phtoth/A320Overhead/Eletronics/Korry_Circuit/korry_circuit_3D_top.PNG

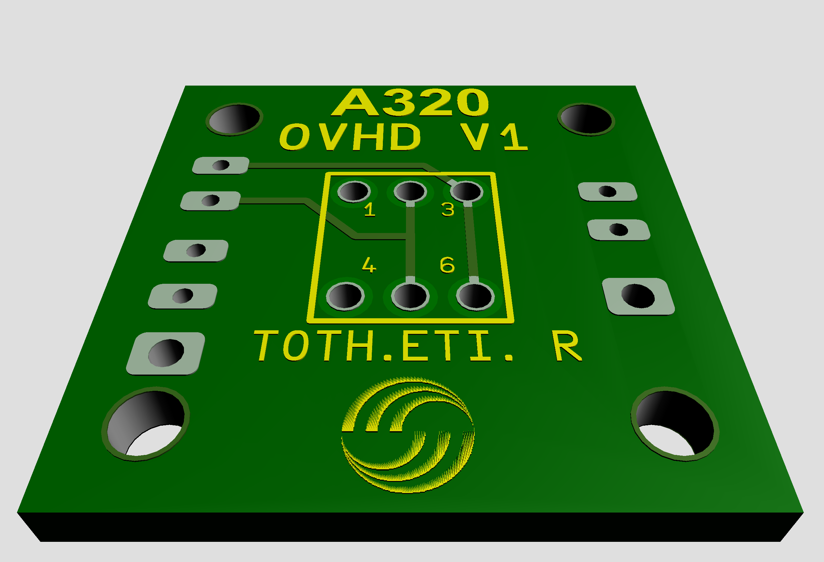
Eletronics/Korry_Circuit/korry_circuit_3D_top.PNG
