phtoth/A320Overhead/Images that Help/ard-mega-pro_io_zc_1024x1024.jpg

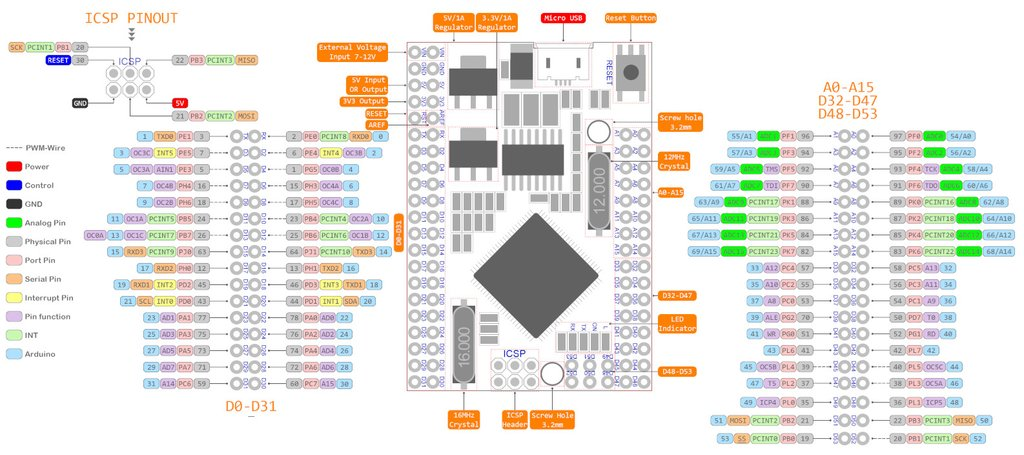
Images that Help/ard-mega-pro_io_zc_1024x1024.jpg
