phtoth/A320Overhead/Images that Help/chave_botao_7x7_des-500x500-product_popup.jpg

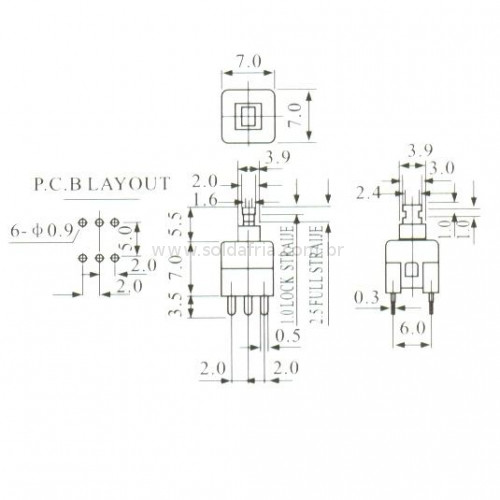
Images that Help/chave_botao_7x7_des-500x500-product_popup.jpg
