phtoth/A320Overhead/Images that Help/images.jpg

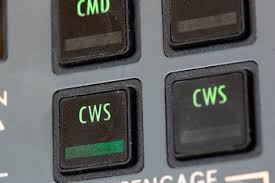
Images that Help/images.jpg
