phtoth/A320Overhead/Images that Help/IMG_1794.jpg

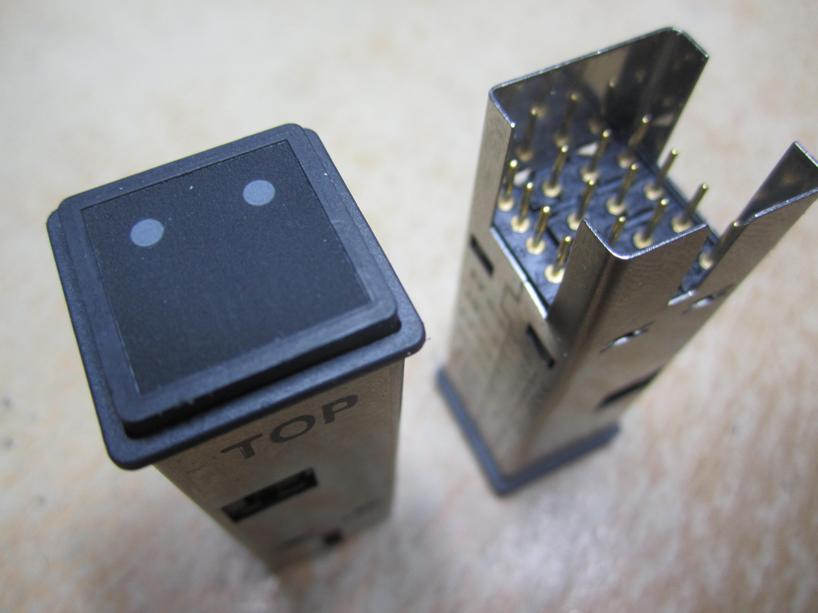
Images that Help/IMG_1794.jpg
