phtoth/A320Overhead/Images that Help/korry-announciator.jpg

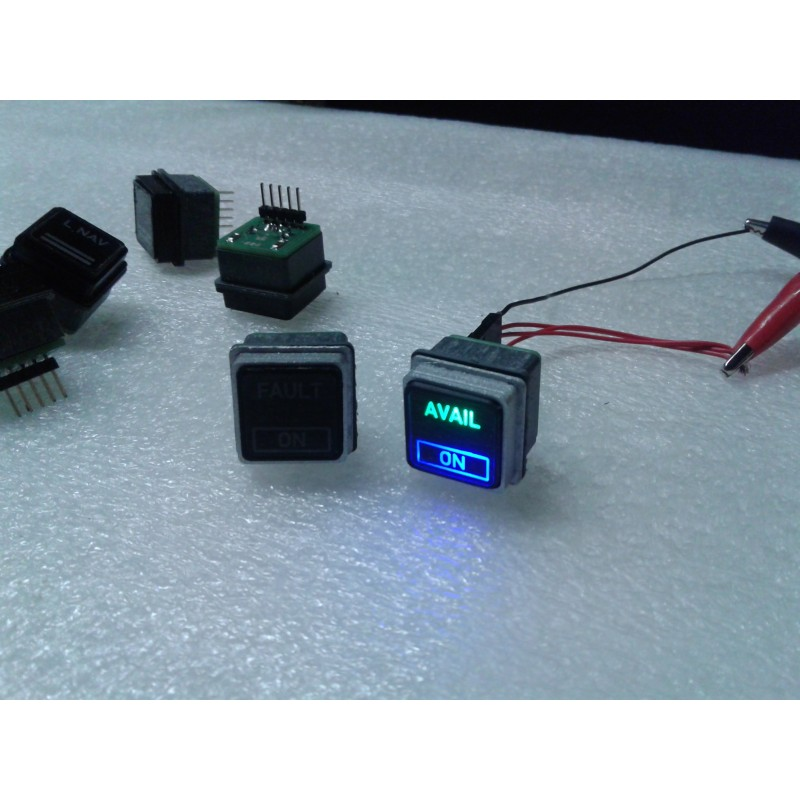
Images that Help/korry-announciator.jpg
