phtoth/A320Overhead/Images that Help/Korry-Switch-Inside-Render.png

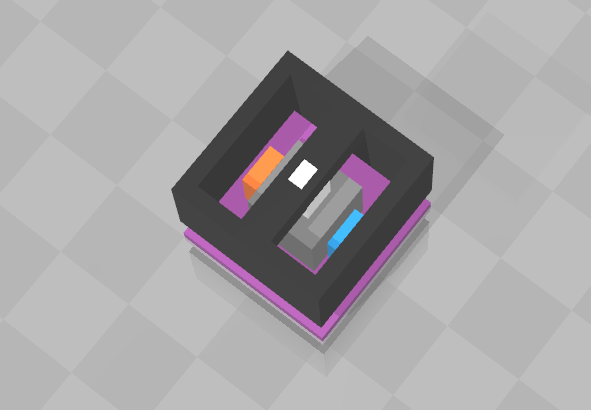
Images that Help/Korry-Switch-Inside-Render.png
