phtoth/A320Overhead/Images that Help/overhead_pic2.jpg

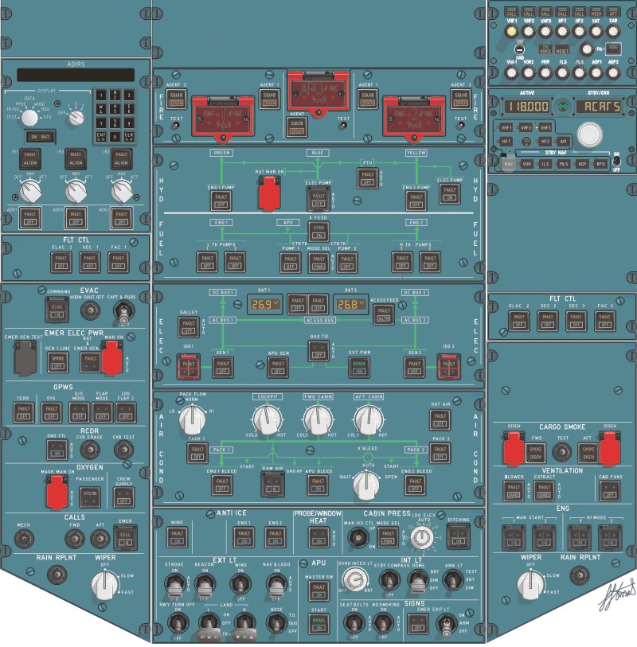
Images that Help/overhead_pic2.jpg
