phtoth/A320Overhead/Korry Switch/Base Korry_ditch v7.obj

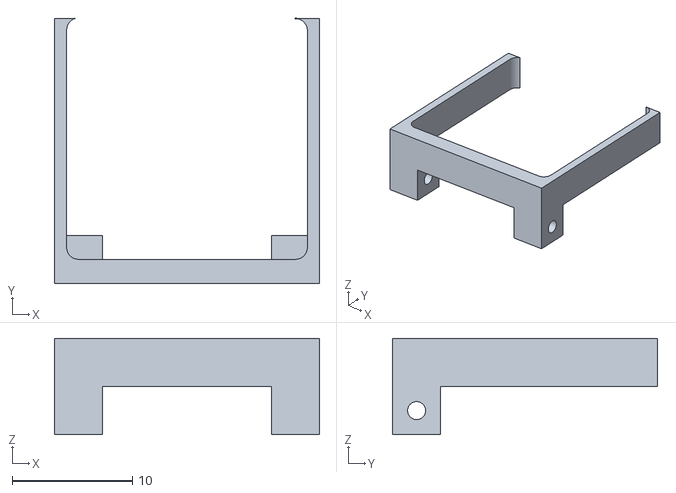
[picture p45: CAD file, 2019-10-23]
Korry Switch/Base Korry_ditch v7.obj
22.0 x 22.0 x 8.00
