phtoth/A320Overhead/Panels/AirCond/Air Cond v13.dxf

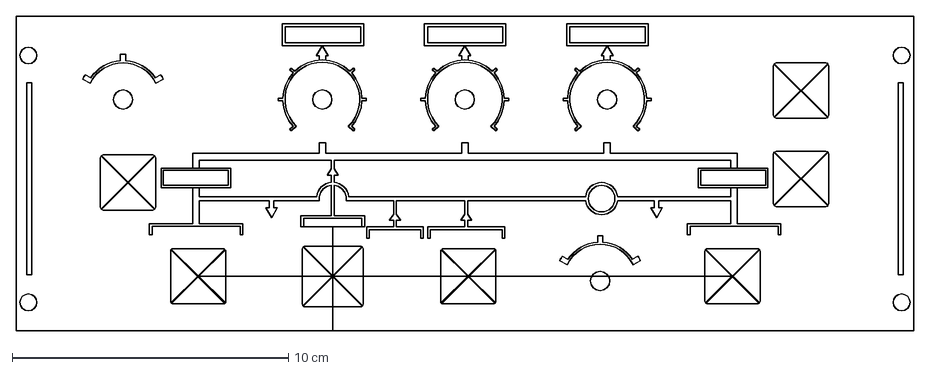
[picture p46: CAD file, 2019-10-23]
Panels/AirCond/Air Cond v13.dxf
32.5 x 11.4 cm
