phtoth/A320Overhead/Panels/AirCond/Cut/AirCond Panel.dxf

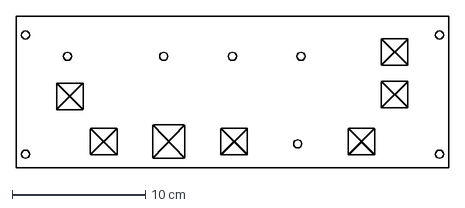
[picture p47: CAD file, 2020-04-19]
Panels/AirCond/Cut/AirCond Panel.dxf
32.5 x 11.4 cm
