phtoth/A320Overhead/Panels/Elec/Cut/Elec Panel.dxf

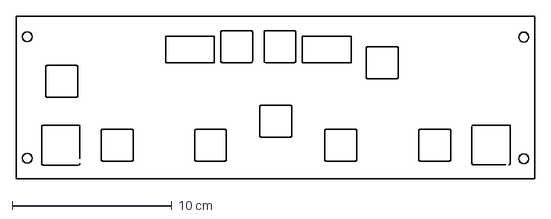
[picture p48: CAD file, 2020-04-19]
Panels/Elec/Cut/Elec Panel.dxf
32.5 x 10.2 cm
