phtoth/A320Overhead/Panels/Fire/Cut/Fire Panel.dxf

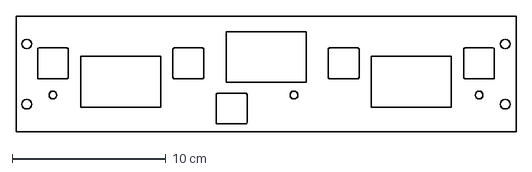
[picture p49: CAD file, 2020-04-21]
Panels/Fire/Cut/Fire Panel.dxf
32.5 x 7.50 cm
