phtoth/A320Overhead/Panels/Hyd_Fuel/Cut/Hyd_Fuel.dxf

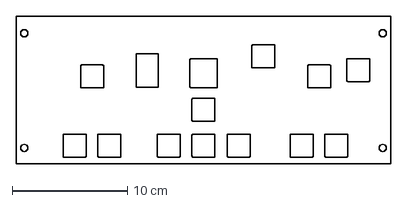
[picture p50: CAD file, 2020-04-21]
Panels/Hyd_Fuel/Cut/Hyd_Fuel.dxf
32.5 x 12.8 cm
