phtoth/A320Overhead/Panels/Left Panel/L_ADIRS/Cut/L_ADIRS Panel.dxf

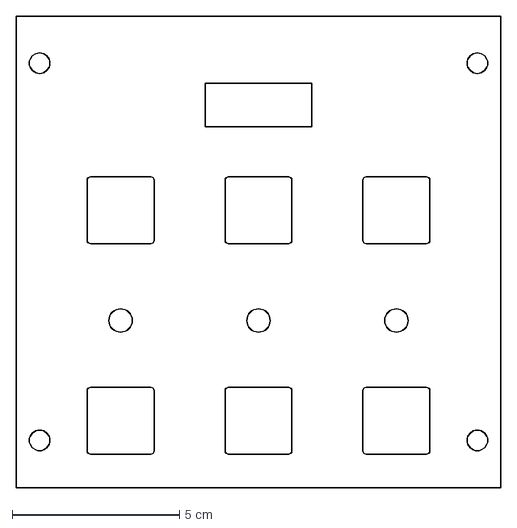
[picture p51: CAD file, 2020-04-23]
Panels/Left Panel/L_ADIRS/Cut/L_ADIRS Panel.dxf
14.5 x 14.1 cm
