phtoth/A320Overhead/Panels/Left Panel/L_BAT/Cut/ON_BAT Panel.dxf

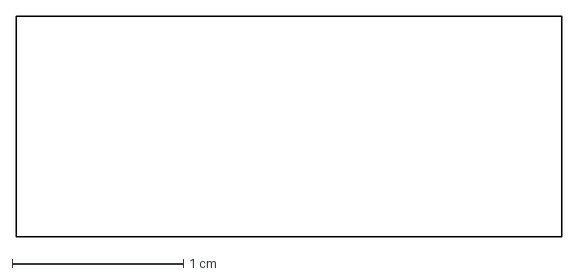
[picture p52: CAD file, 2020-05-17]
Panels/Left Panel/L_BAT/Cut/ON_BAT Panel.dxf
3.19 x 1.29 cm
