phtoth/A320Overhead/Panels/Left Panel/L_Blank/Cut/L_Blank Panel.dxf

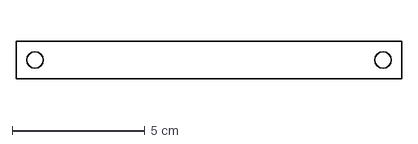
[picture p53: CAD file, 2020-04-23]
Panels/Left Panel/L_Blank/Cut/L_Blank Panel.dxf
14.5 x 1.40 cm
