phtoth/A320Overhead/Panels/Left Panel/L_Cargo_Smoke/Cut/L_Cargo_Smoke Panel.dxf

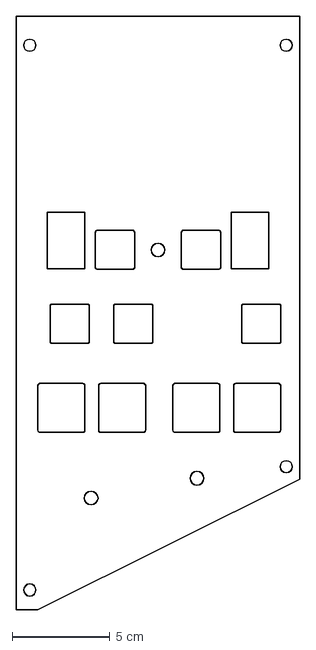
[picture p54: CAD file, 2020-04-21]
Panels/Left Panel/L_Cargo_Smoke/Cut/L_Cargo_Smoke Panel.dxf
14.5 x 30.3 cm
