phtoth/A320Overhead/Panels/Left Panel/L_EVAC/Cut/L_EVAC Panel.dxf

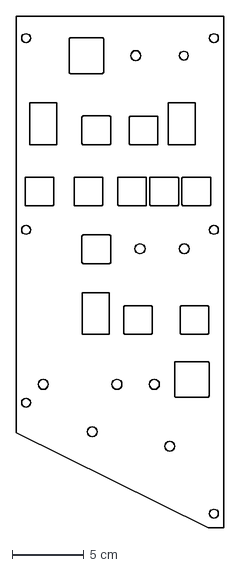
[picture p55: CAD file, 2020-05-13]
Panels/Left Panel/L_EVAC/Cut/L_EVAC Panel.dxf
14.5 x 35.7 cm
