phtoth/A320Overhead/Panels/Left Panel/L_FLT_CTL/Cut/L_FLT_CTL Panel.dxf

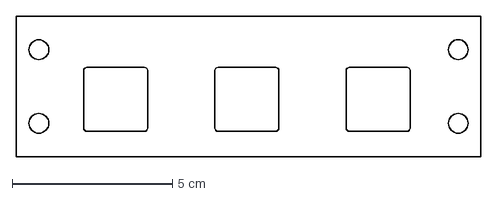
[picture p56: CAD file, 2020-04-23]
Panels/Left Panel/L_FLT_CTL/Cut/L_FLT_CTL Panel.dxf
14.5 x 4.40 cm
