phtoth/A320Overhead/Panels/Left Panel/L_Radio_01_Blank/Cut/L_Radio_01_Blank Panel.dxf

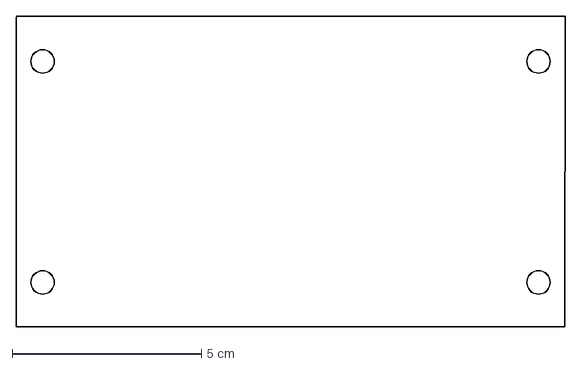
[picture p57: CAD file, 2020-04-21]
Panels/Left Panel/L_Radio_01_Blank/Cut/L_Radio_01_Blank Panel.dxf
14.5 x 8.20 cm
