phtoth/A320Overhead/Panels/Left Panel/L_Radio_02_Blank/Cut/L_Radio_02_Blank Panel.dxf

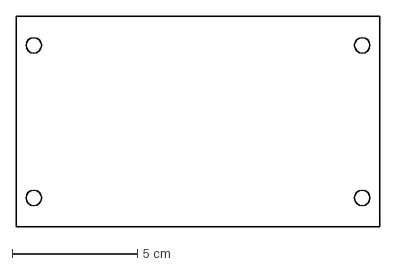
[picture p58: CAD file, 2020-04-21]
Panels/Left Panel/L_Radio_02_Blank/Cut/L_Radio_02_Blank Panel.dxf
14.5 x 8.40 cm
