phtoth/A320Overhead/Panels/Light/Cut/light panel.dxf

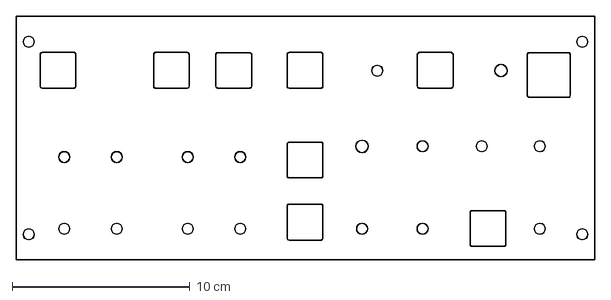
[picture p59: CAD file, 2020-04-19]
Panels/Light/Cut/light panel.dxf
32.5 x 13.7 cm
