phtoth/A320Overhead/Panels/Light/Luzes v34.dxf

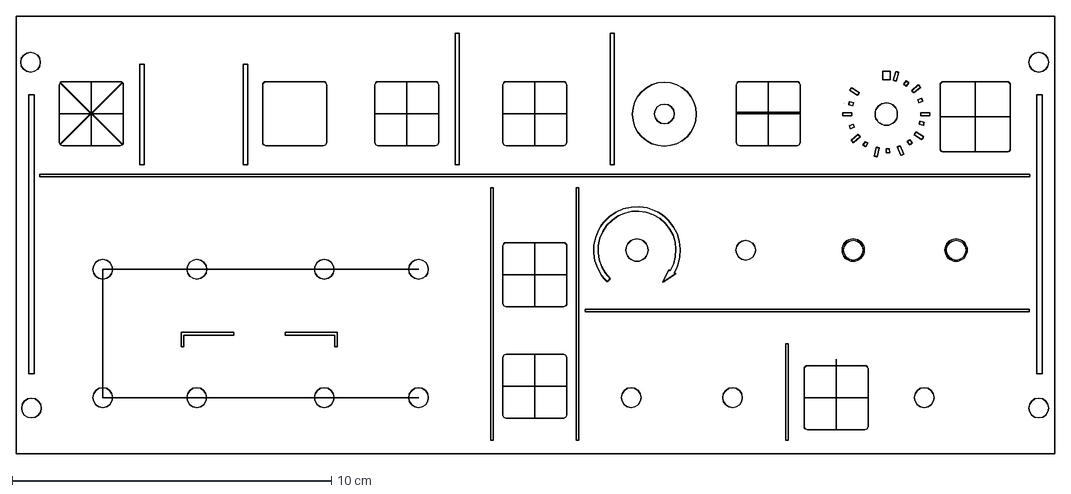
[picture p60: CAD file, 2019-08-21]
Panels/Light/Luzes v34.dxf
32.5 x 13.7 cm
