phtoth/A320Overhead/Panels/Right Panel/R_FLT_CTL/Cut/R_FLT_CTL Panel.dxf

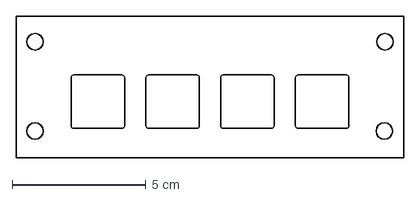
[picture p61: CAD file, 2020-04-21]
Panels/Right Panel/R_FLT_CTL/Cut/R_FLT_CTL Panel.dxf
14.5 x 5.30 cm
