phtoth/A320Overhead/A320 AutoCAD Project/cubo_vivo v1.obj

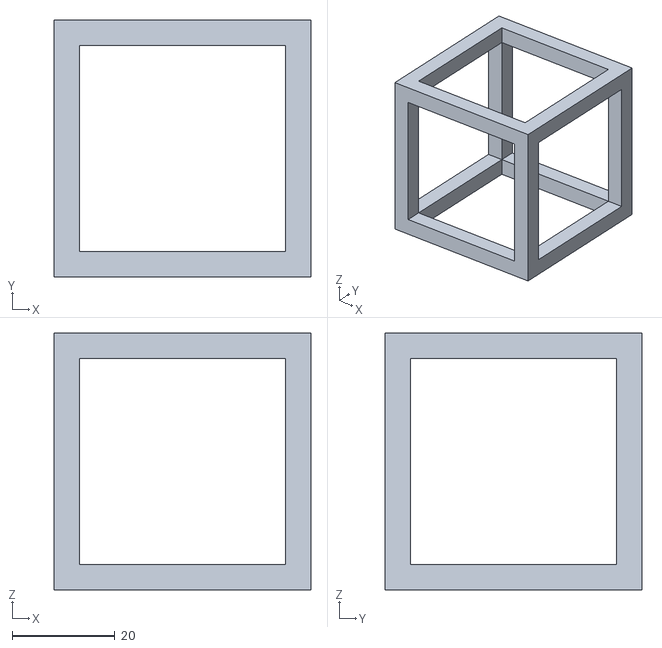
[picture p62: CAD file, 2019-10-23]
A320 AutoCAD Project/cubo_vivo v1.obj
50.0 x 50.0 x 50.0
