phtoth/A320Overhead/Korry Switch/Base Korry v24.obj

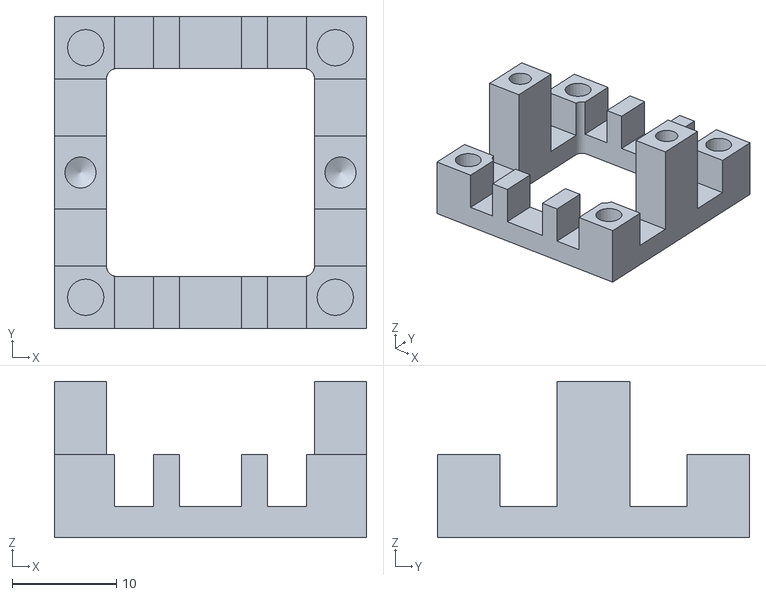
[picture p63: CAD file, 2019-08-21]
Korry Switch/Base Korry v24.obj
30.0 x 30.0 x 15.0
