phtoth/A320Overhead/Panels/Extra Size/Cut/Extra_Side.dxf

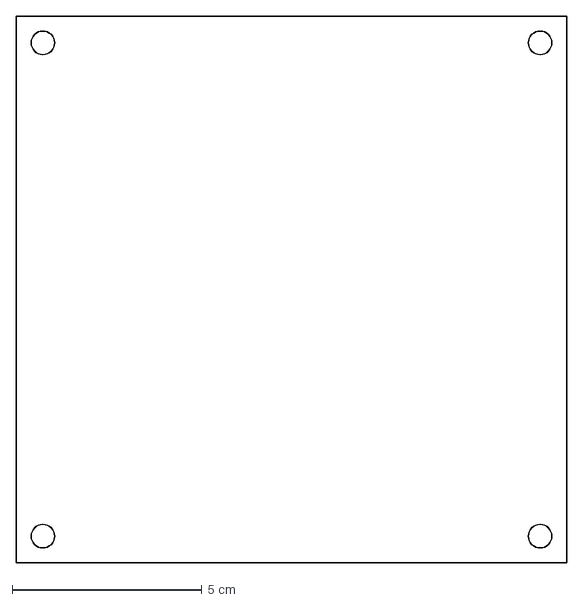
[picture p64: CAD file, 2020-05-17]
Panels/Extra Size/Cut/Extra_Side.dxf
14.5 x 14.4 cm
