phtoth/A320Overhead/Eletronics/Korry_Circuit/korry_circuit_copper_all_layers.pdf

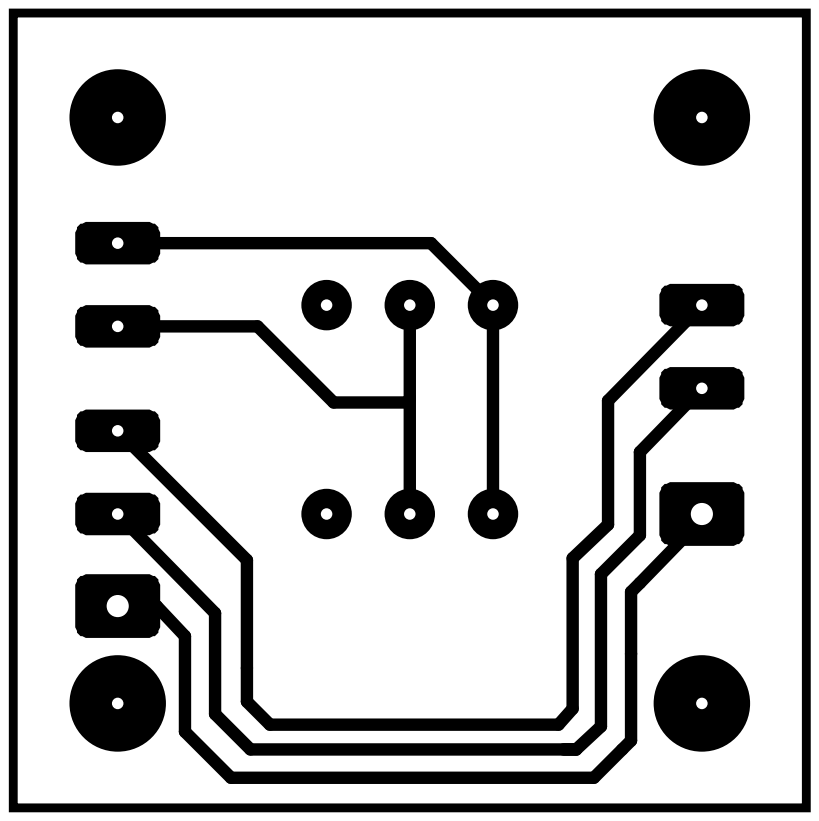
[picture p74: page 1]
