phtoth/A320Overhead/Eletronics/Korry_Circuit/korry_circuit_copper_bottom.pdf

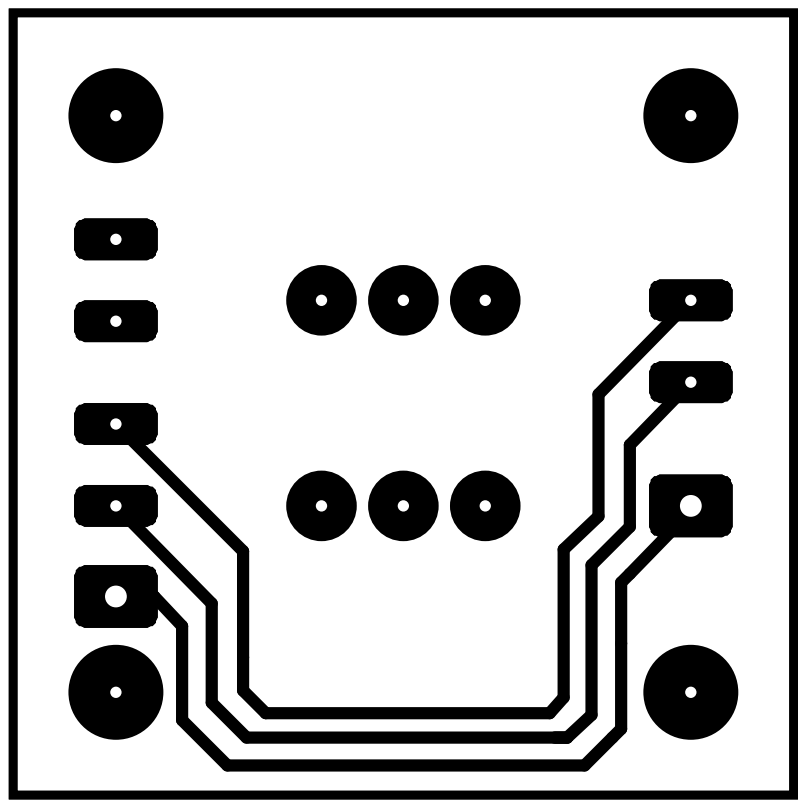
[picture p75: page 1]
