phtoth/A320Overhead/Eletronics/Korry_Circuit/korry_circuit_copper_top.pdf

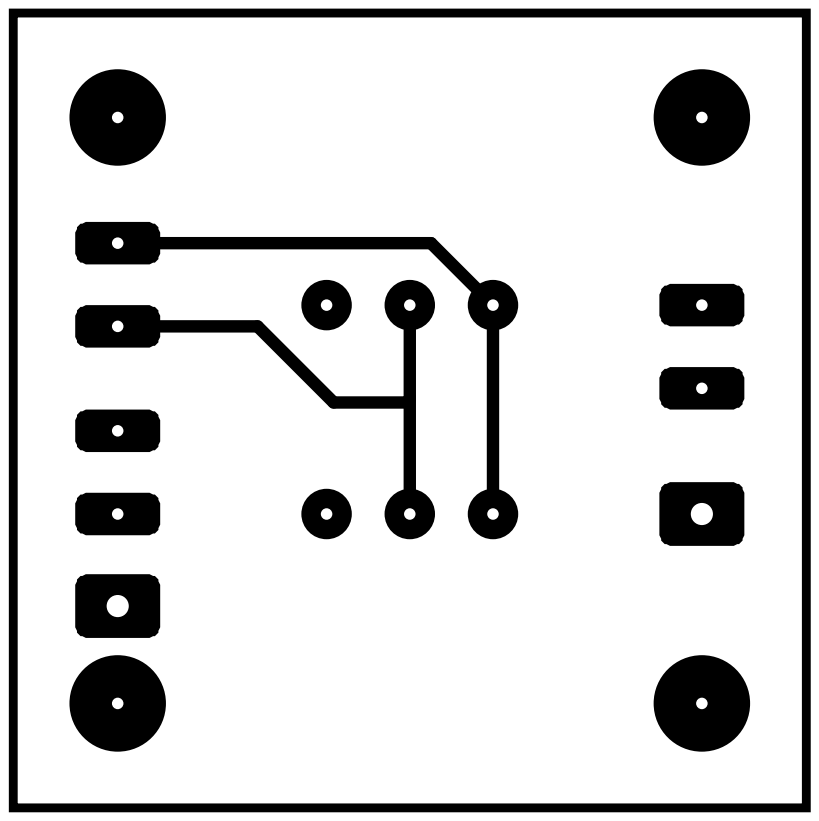
[picture p76: page 1]
